Pirate-MIDI/Polar/Polar Pico/DSC02058.jpg

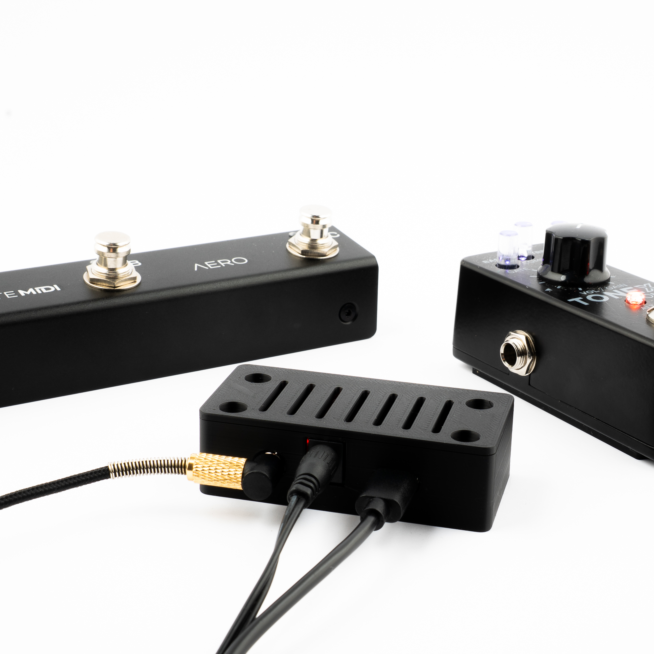
Polar Pico/DSC02058.jpg
